411568/Universal_interface_adapter/GPIO.kicad_sch

## KiCad design GPIO.kicad_sch (2026-03-23)

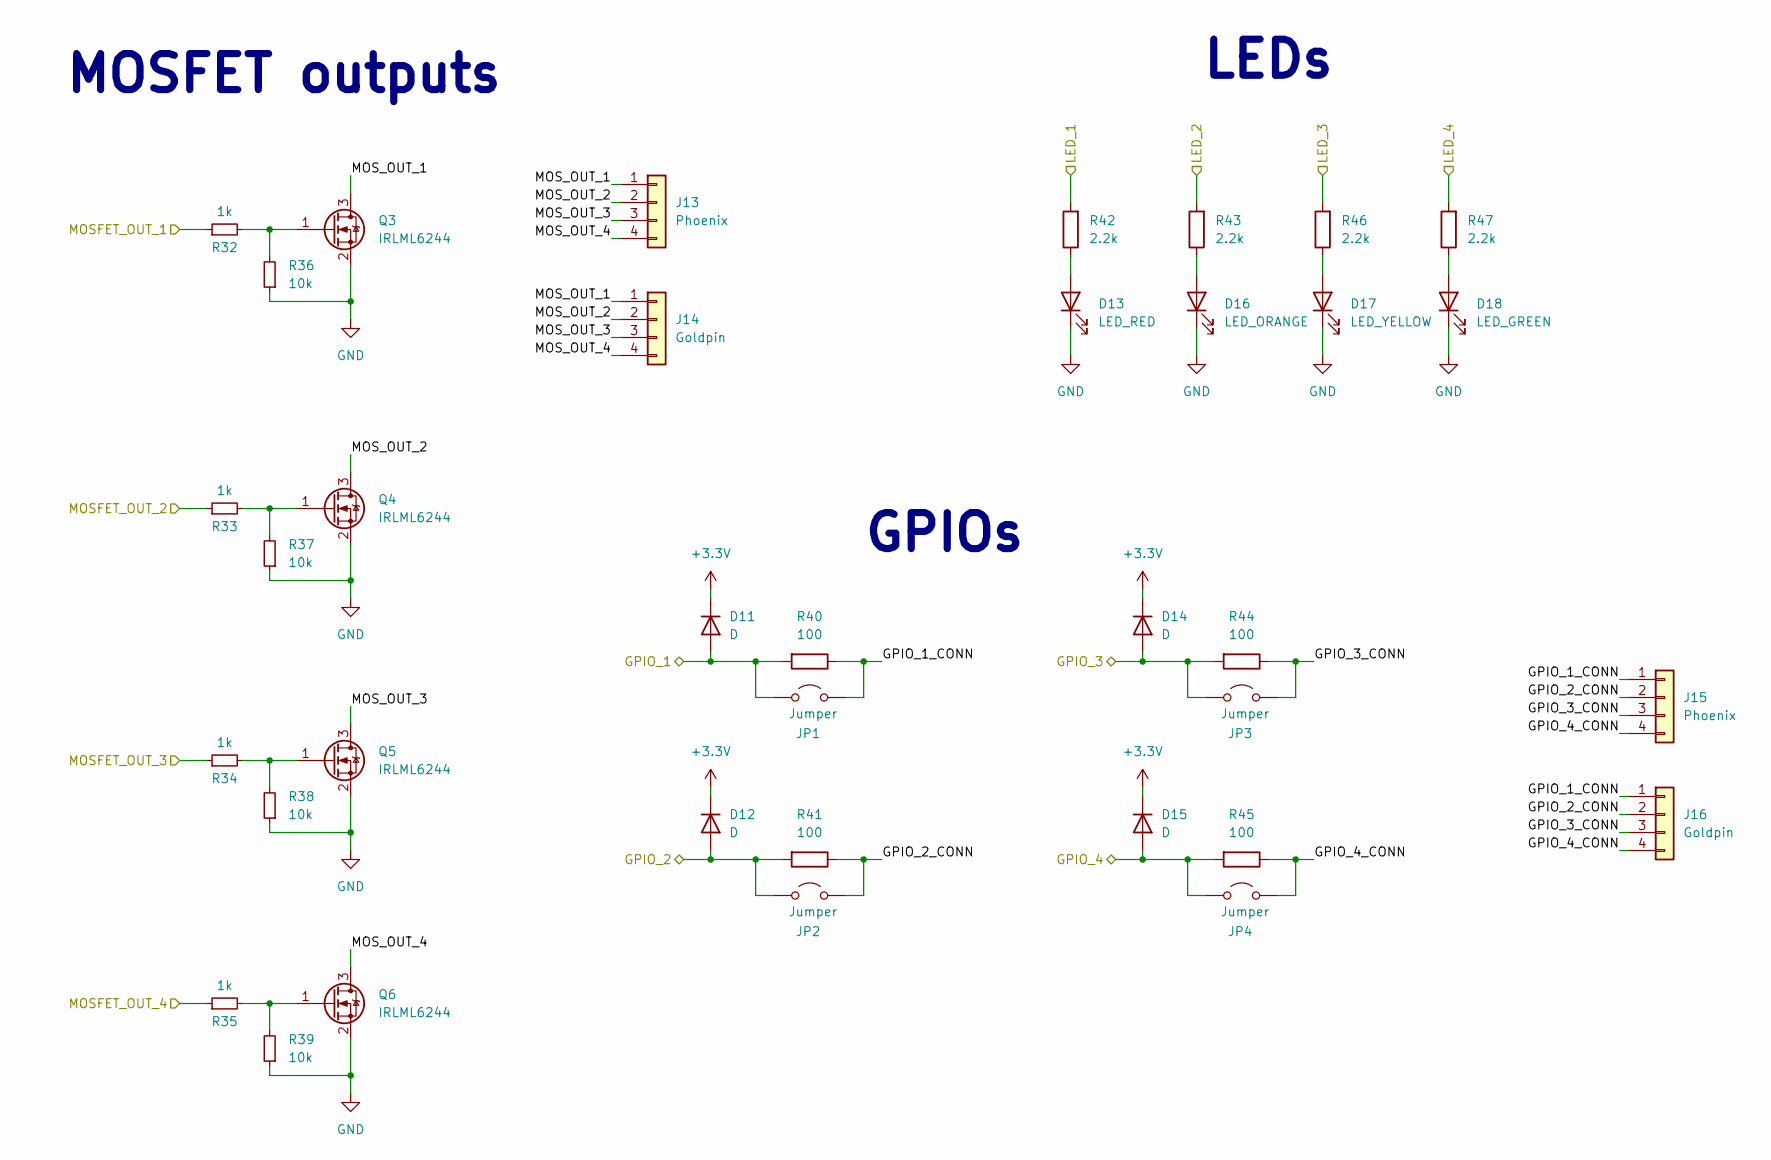
[picture p10: schematic GPIO.kicad_sch]

Parts:
D11, D12, D14, D15: D; D_SMA_Handsoldering
D13: LED_RED; LED_0805_2012Metric_Pad1.15x1.40mm_HandSolder
D16: LED_ORANGE; LED_0805_2012Metric_Pad1.15x1.40mm_HandSolder
D17: LED_YELLOW; LED_0805_2012Metric_Pad1.15x1.40mm_HandSolder
D18: LED_GREEN; LED_0805_2012Metric_Pad1.15x1.40mm_HandSolder
J13, J15: Phoenix; PhoenixContact_MC_1,5_4-G-3.5_1x04_P3.50mm_Horizontal
J14, J16: Goldpin; PinHeader_1x04_P2.54mm_Vertical
JP1, JP2, JP3, JP4: Jumper; PinHeader_1x02_P2.54mm_Vertical
Q3, Q4, Q5, Q6: IRLML6244; SOT-23
R32, R33, R34, R35: 1k; R_0805_2012Metric_Pad1.20x1.40mm_HandSolder
R36, R37, R38, R39: 10k; R_0805_2012Metric_Pad1.20x1.40mm_HandSolder
R40, R41, R44, R45: 100; R_0805_2012Metric_Pad1.20x1.40mm_HandSolder
R42, R43, R46, R47: 2.2k; R_0805_2012Metric_Pad1.20x1.40mm_HandSolder

Connections:
+3.3V: D11.1 (K), D12.1 (K), D14.1 (K), D15.1 (K)
GND: D13.1 (K), D16.1 (K), D17.1 (K), D18.1 (K), Q3.2 (S), Q4.2 (S), Q5.2 (S), Q6.2 (S), R36.1, R37.1, R38.1, R39.1
GPIO_1: D11.2 (A), JP1.1 (A), R40.2
GPIO_1_CONN: J15.1, J16.1, JP1.2 (B), R40.1
GPIO_2: D12.2 (A), JP2.1 (A), R41.2
GPIO_2_CONN: J15.2, J16.2, JP2.2 (B), R41.1
GPIO_3: D14.2 (A), JP3.1 (A), R44.2
GPIO_3_CONN: J15.3, J16.3, JP3.2 (B), R44.1
GPIO_4: D15.2 (A), JP4.1 (A), R45.2
GPIO_4_CONN: J15.4, J16.4, JP4.2 (B), R45.1
LED_1: R42.2
LED_2: R43.2
LED_3: R46.2
LED_4: R47.2
MOSFET_OUT_1: R32.1
MOSFET_OUT_2: R33.1
MOSFET_OUT_3: R34.1
MOSFET_OUT_4: R35.1
MOS_OUT_1: J13.1, J14.1, Q3.3 (D)
MOS_OUT_2: J13.2, J14.2, Q4.3 (D)
MOS_OUT_3: J13.3, J14.3, Q5.3 (D)
MOS_OUT_4: J13.4, J14.4, Q6.3 (D)
unnamed: D13.2 (A), R42.1
unnamed: D16.2 (A), R43.1
unnamed: D17.2 (A), R46.1
unnamed: D18.2 (A), R47.1
unnamed: Q3.1 (G), R32.2, R36.2
unnamed: Q4.1 (G), R33.2, R37.2
unnamed: Q5.1 (G), R34.2, R38.2
unnamed: Q6.1 (G), R35.2, R39.2

Notes on the sheet:
MOSFET outputs
GPIOs
LEDs
