411568/Universal_interface_adapter/analog.kicad_sch

## KiCad design analog.kicad_sch (2026-03-23)

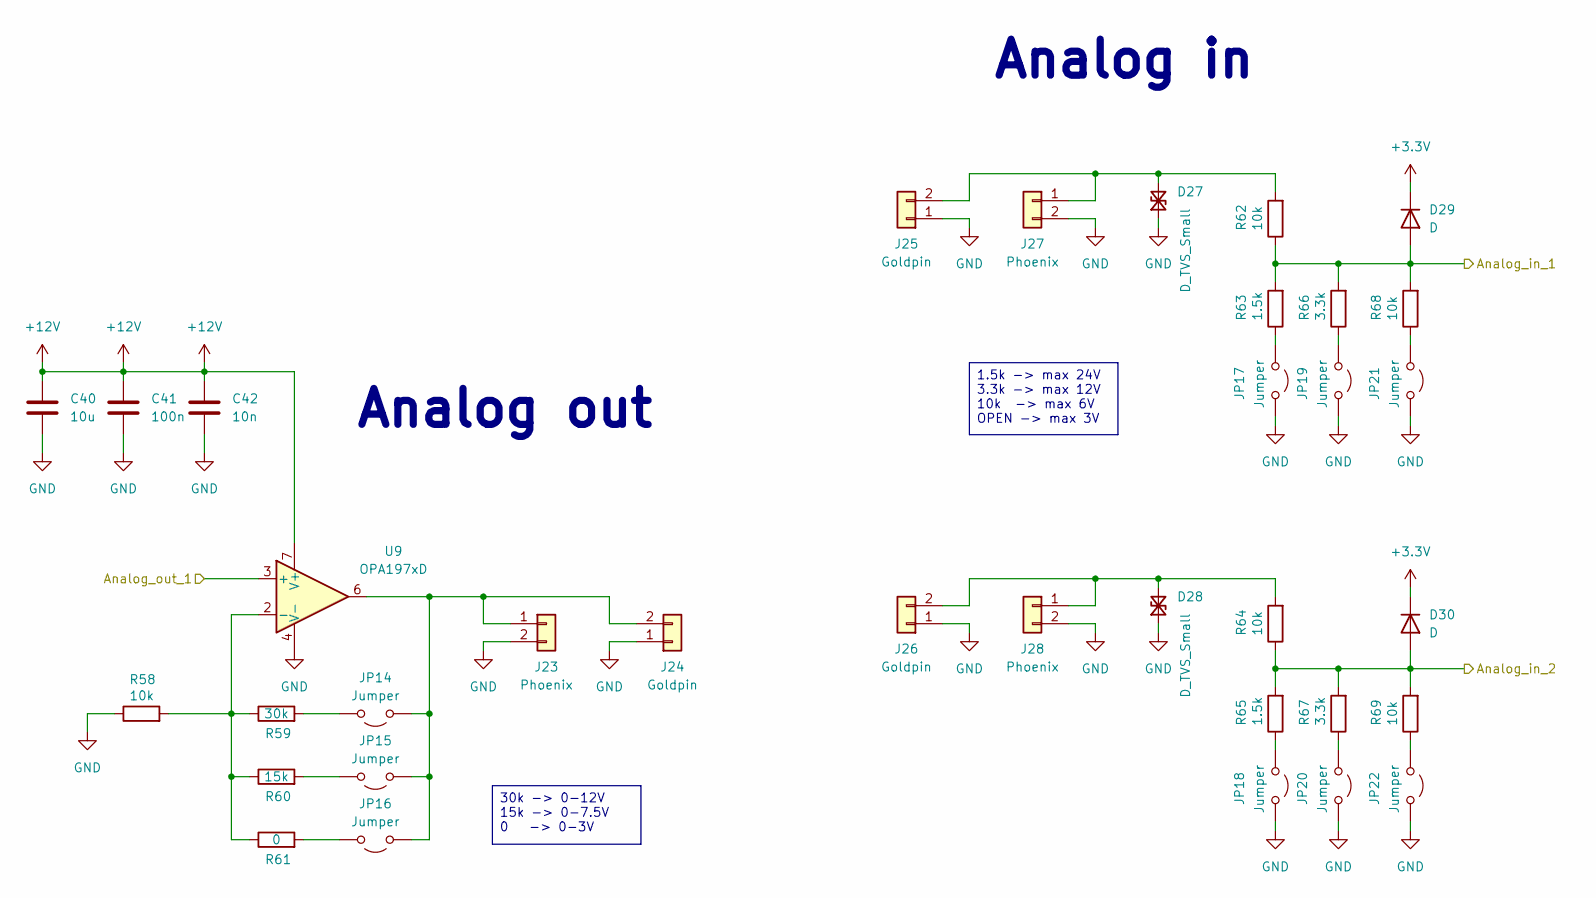
[picture p11: schematic analog.kicad_sch]

Parts:
C40: 10u; C_1206_3216Metric_Pad1.33x1.80mm_HandSolder
C41: 100n; C_1206_3216Metric_Pad1.33x1.80mm_HandSolder
C42: 10n; C_0805_2012Metric_Pad1.18x1.45mm_HandSolder
D27, D28: D_TVS_Small; D_SMA_Handsoldering
D29, D30: D; D_SMA_Handsoldering
J23, J27, J28: Phoenix; PhoenixContact_MC_1,5_2-G-3.5_1x02_P3.50mm_Horizontal
J24, J25, J26: Goldpin; PinHeader_1x02_P2.54mm_Vertical
JP14, JP15, JP16, JP17, JP18, JP19, JP20, JP21, JP22: Jumper; PinHeader_1x02_P2.54mm_Vertical
R58, R62, R64, R68, R69: 10k; R_0805_2012Metric_Pad1.20x1.40mm_HandSolder
R59: 30k; R_0805_2012Metric_Pad1.20x1.40mm_HandSolder
R60: 15k; R_0805_2012Metric_Pad1.20x1.40mm_HandSolder
R61: 0; R_0805_2012Metric_Pad1.20x1.40mm_HandSolder
R63, R65: 1.5k; R_0805_2012Metric_Pad1.20x1.40mm_HandSolder
R66, R67: 3.3k; R_0805_2012Metric_Pad1.20x1.40mm_HandSolder
U9: OPA197xD; SOIC-8_3.9x4.9mm_P1.27mm

Connections:
+3.3V: D29.1 (K), D30.1 (K)
+12V: C40.1, C41.1, C42.1, U9.7 (V+)
Analog_in_1: D29.2 (A), R62.1, R63.2, R66.2, R68.2
Analog_in_2: D30.2 (A), R64.1, R65.2, R67.2, R69.2
Analog_out_1: U9.3 (+)
GND: C40.2, C41.2, C42.2, D27.1 (A1), D28.1 (A1), J23.2, J24.1, J25.1, J26.1, J27.2, J28.2, JP17.2 (B), JP18.2 (B), JP19.2 (B), JP20.2 (B), JP21.2 (B), JP22.2 (B), R58.1, U9.4 (V-)
unnamed: D27.2 (A2), J25.2, J27.1, R62.2
unnamed: D28.2 (A2), J26.2, J28.1, R64.2
unnamed: J23.1, J24.2, JP14.1 (A), JP15.1 (A), JP16.1 (A), U9.6
unnamed: JP14.2 (B), R59.2
unnamed: JP15.2 (B), R60.2
unnamed: JP16.2 (B), R61.2
unnamed: JP17.1 (A), R63.1
unnamed: JP18.1 (A), R65.1
unnamed: JP19.1 (A), R66.1
unnamed: JP20.1 (A), R67.1
unnamed: JP21.1 (A), R68.1
unnamed: JP22.1 (A), R69.1
unnamed: R58.2, R59.1, R60.1, R61.1, U9.2 (-)

Notes on the sheet:
Analog out
Analog in
30k -> 0-12V 15k -> 0-7.5V 0 -> 0-3V
1.5k -> max 24V 3.3k -> max 12V 10k -> max 6V OPEN -> max 3V
