411568/Universal_interface_adapter/can.kicad_sch

## KiCad design can.kicad_sch (2026-03-23)

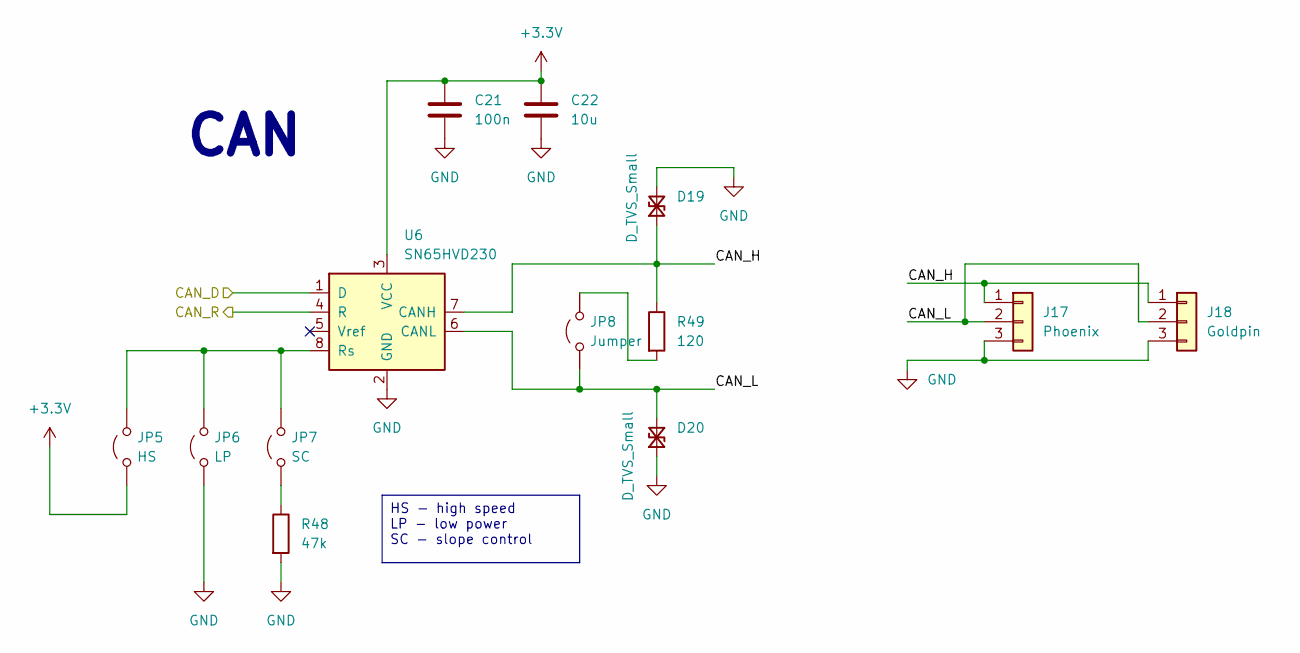
[picture p12: schematic can.kicad_sch]

Parts:
C21: 100n; C_0805_2012Metric_Pad1.18x1.45mm_HandSolder
C22: 10u; C_0805_2012Metric_Pad1.18x1.45mm_HandSolder
D19, D20: D_TVS_Small; D_SMA_Handsoldering
J17: Phoenix; PhoenixContact_MC_1,5_3-G-3.5_1x03_P3.50mm_Horizontal
J18: Goldpin; PinHeader_1x03_P2.54mm_Vertical
JP5: HS; PinHeader_1x02_P2.54mm_Vertical
JP6: LP; PinHeader_1x02_P2.54mm_Vertical
JP7: SC; PinHeader_1x02_P2.54mm_Vertical
JP8: Jumper; PinHeader_1x02_P2.54mm_Vertical
R48: 47k; R_1206_3216Metric_Pad1.30x1.75mm_HandSolder
R49: 120; R_1206_3216Metric_Pad1.30x1.75mm_HandSolder
U6: SN65HVD230; SOIC-8_3.9x4.9mm_P1.27mm

Connections:
+3.3V: C21.1, C22.1, JP5.1 (A), U6.3 (VCC)
CAN_D: U6.1 (D)
CAN_H: D19.1 (A1), J17.1, J18.1, R49.1, U6.7 (CANH)
CAN_L: D20.2 (A2), J17.2, J18.2, JP8.1 (A), U6.6 (CANL)
CAN_R: U6.4 (R)
GND: C21.2, C22.2, D19.2 (A2), D20.1 (A1), J17.3, J18.3, JP6.1 (A), R48.2, U6.2 (GND)
unnamed: JP5.2 (B), JP6.2 (B), JP7.2 (B), U6.8 (Rs)
unnamed: JP7.1 (A), R48.1
unnamed: JP8.2 (B), R49.2

Notes on the sheet:
CAN
HS - high speed LP - low power SC - slope control
