411568/Universal_interface_adapter/isolated_inputs.kicad_sch

## KiCad design isolated_inputs.kicad_sch (2026-03-23)

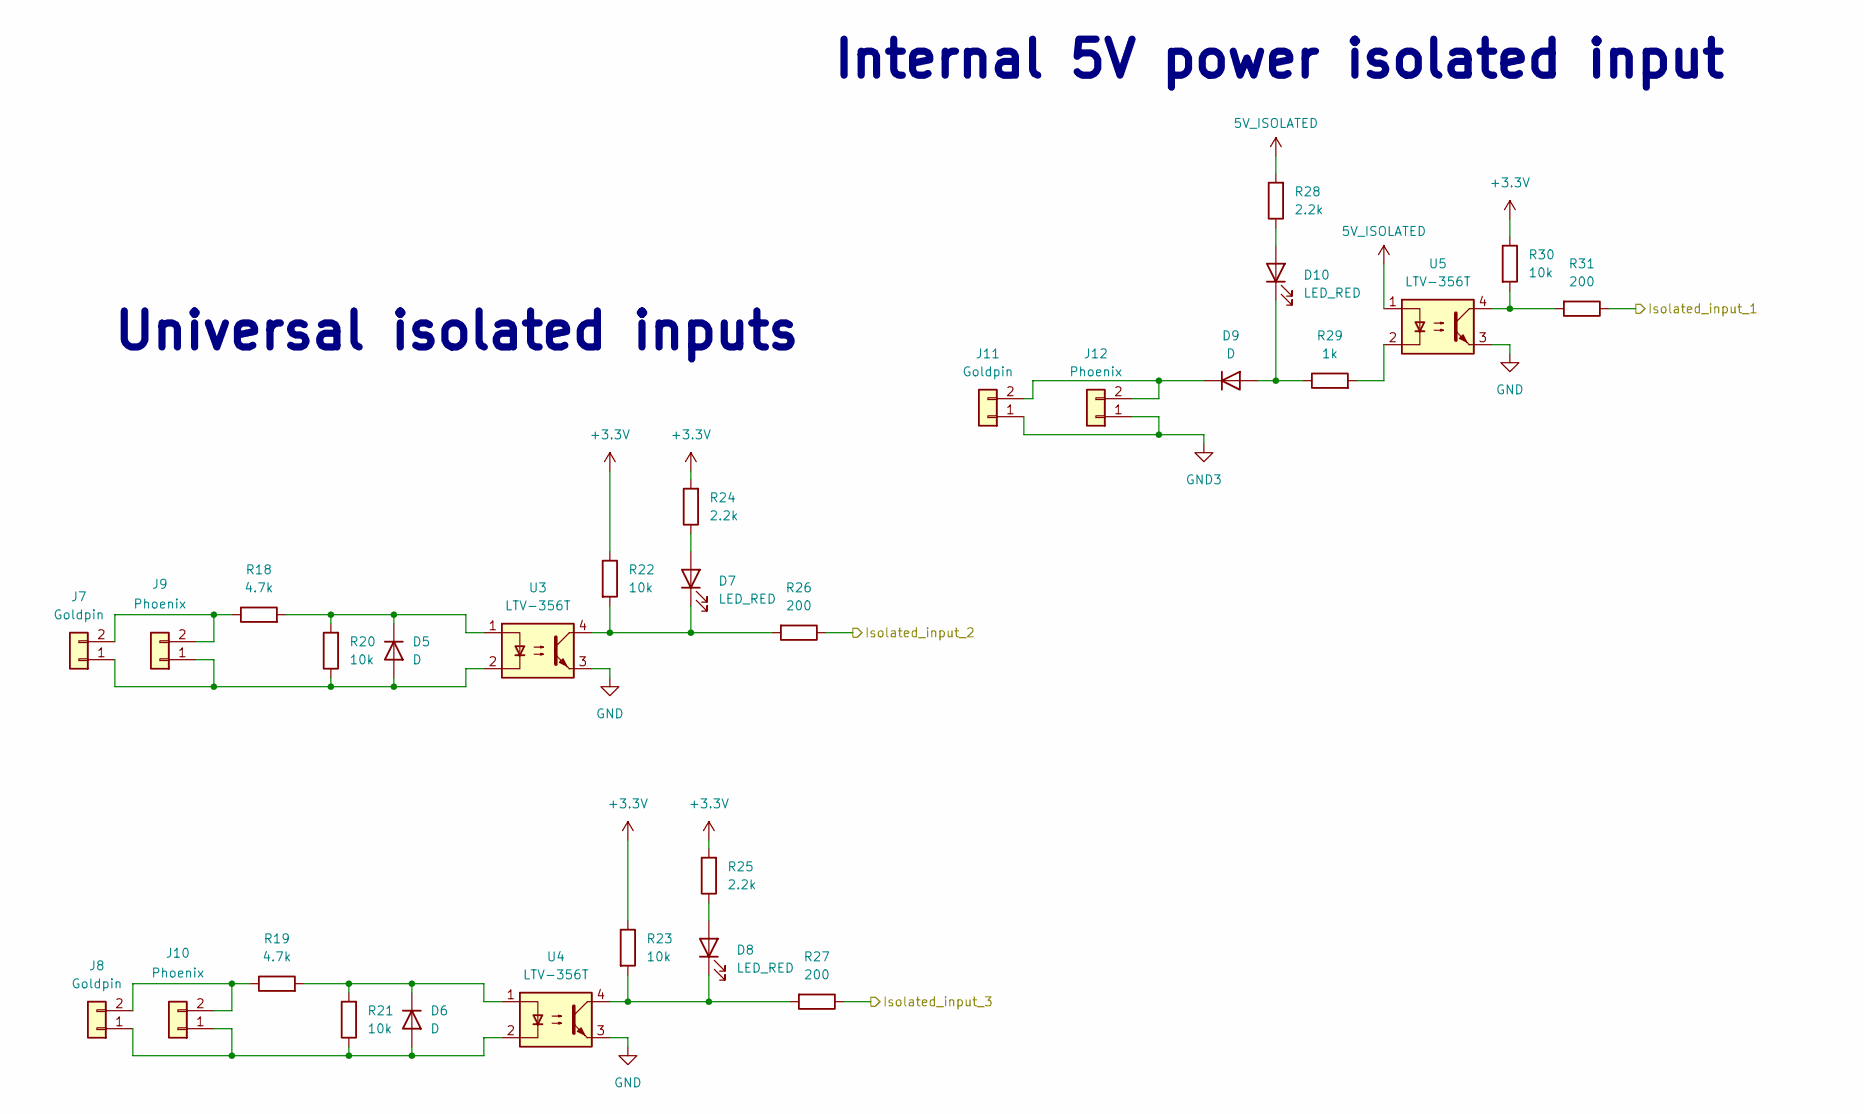
[picture p13: schematic isolated_inputs.kicad_sch]

Parts:
D5, D6, D9: D; D_SMA_Handsoldering
D7, D8, D10: LED_RED; LED_0805_2012Metric_Pad1.15x1.40mm_HandSolder
J7, J8, J11: Goldpin; PinHeader_1x02_P2.54mm_Vertical
J9, J10, J12: Phoenix; PhoenixContact_MC_1,5_2-G-3.5_1x02_P3.50mm_Horizontal
R18, R19: 4.7k; R_0805_2012Metric_Pad1.20x1.40mm_HandSolder
R20, R21, R22, R23, R30: 10k; R_0805_2012Metric_Pad1.20x1.40mm_HandSolder
R24, R25, R28: 2.2k; R_0805_2012Metric_Pad1.20x1.40mm_HandSolder
R26, R27, R31: 200; R_0805_2012Metric_Pad1.20x1.40mm_HandSolder
R29: 1k; R_0805_2012Metric_Pad1.20x1.40mm_HandSolder
U3, U4, U5: LTV-356T; SO-4_4.4x3.6mm_P2.54mm

Connections:
5V_ISOLATED: R28.2, U5.1
+3.3V: R22.1, R23.1, R24.2, R25.2, R30.1
GND: U3.3, U4.3, U5.3
GND3: J11.1, J12.1
Isolated_input_1: R31.1
Isolated_input_2: R26.1
Isolated_input_3: R27.1
unnamed: D5.1 (K), R18.2, R20.2, U3.1
unnamed: D5.2 (A), J7.1, J9.1, R20.1, U3.2
unnamed: D6.1 (K), R19.2, R21.2, U4.1
unnamed: D6.2 (A), J8.1, J10.1, R21.1, U4.2
unnamed: D7.1 (K), R22.2, R26.2, U3.4
unnamed: D7.2 (A), R24.1
unnamed: D8.1 (K), R23.2, R27.2, U4.4
unnamed: D8.2 (A), R25.1
unnamed: D9.1 (K), J11.2, J12.2
unnamed: D9.2 (A), D10.1 (K), R29.1
unnamed: D10.2 (A), R28.1
unnamed: J7.2, J9.2, R18.1
unnamed: J8.2, J10.2, R19.1
unnamed: R29.2, U5.2
unnamed: R30.2, R31.2, U5.4

Notes on the sheet:
Universal isolated inputs
Internal 5V power isolated input
