411568/Universal_interface_adapter/power.kicad_sch

## KiCad design power.kicad_sch (2026-03-23)

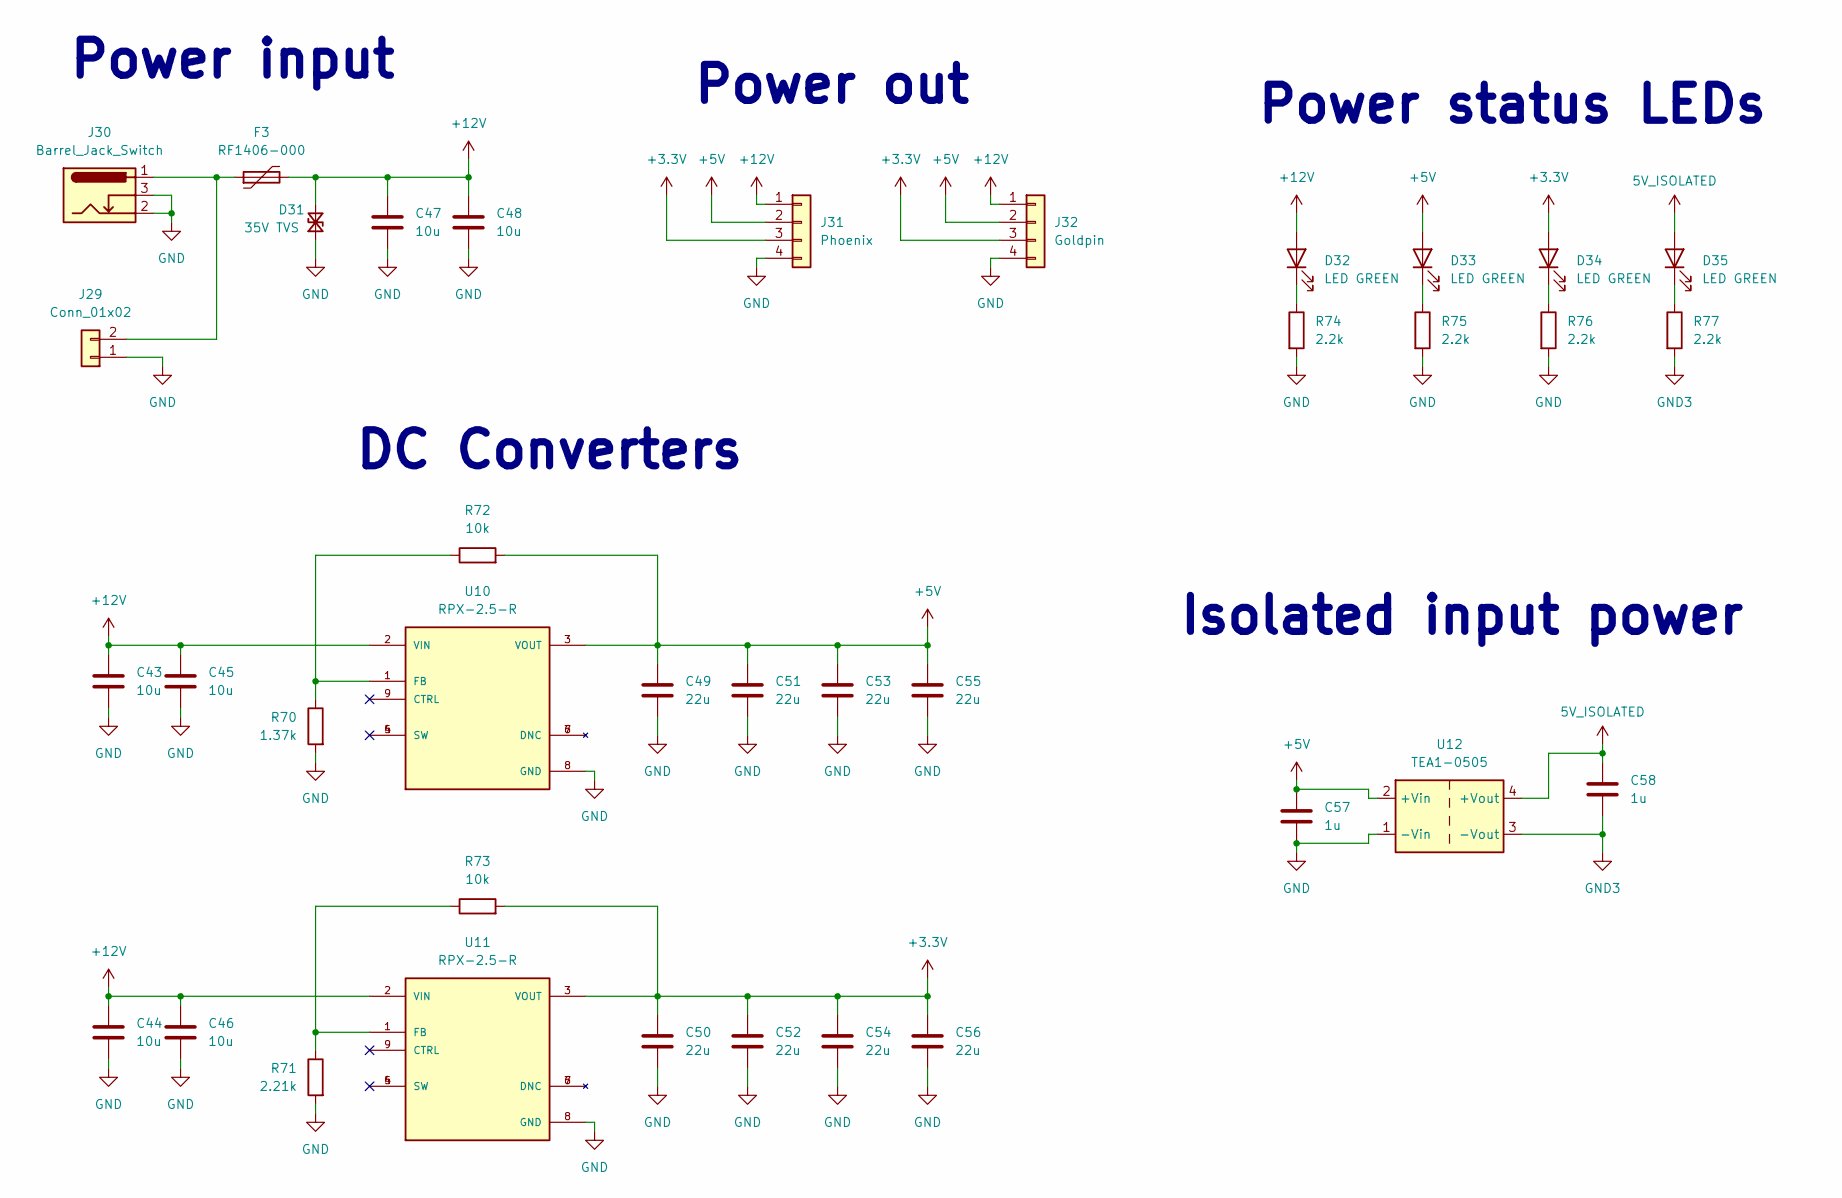
[picture p14: schematic power.kicad_sch]

Parts:
C43, C44, C45, C46, C47, C48: 10u; C_1206_3216Metric_Pad1.33x1.80mm_HandSolder
C49, C50, C51, C52: 22u; C_1206_3216Metric_Pad1.33x1.80mm_HandSolder
C53, C54, C55, C56: 22u; C_0805_2012Metric_Pad1.18x1.45mm_HandSolder
C57, C58: 1u; C_0805_2012Metric_Pad1.18x1.45mm_HandSolder
D31: 35V TVS; D_SMA_Handsoldering
D32, D33, D34, D35: LED GREEN; LED_0805_2012Metric_Pad1.15x1.40mm_HandSolder
F3: RF1406-000; Fuse_1812_4532Metric_Pad1.30x3.40mm_HandSolder
J29: Conn_01x02; PhoenixContact_MC_1,5_2-G-3.5_1x02_P3.50mm_Horizontal
J30: Barrel_Jack_Switch; BarrelJack_GCT_DCJ200-10-A_Horizontal
J31: Phoenix; PhoenixContact_MC_1,5_4-G-3.5_1x04_P3.50mm_Horizontal
J32: Goldpin; PinHeader_1x04_P2.54mm_Vertical
R70: 1.37k; R_0805_2012Metric_Pad1.20x1.40mm_HandSolder
R71: 2.21k; R_0805_2012Metric_Pad1.20x1.40mm_HandSolder
R72, R73: 10k; R_0805_2012Metric_Pad1.20x1.40mm_HandSolder
R74, R75, R76, R77: 2.2k; R_0805_2012Metric_Pad1.20x1.40mm_HandSolder
U10, U11: RPX-2.5-R; CONV_RPX-2.5-R; PARTREV 03/2020
U12: TEA1-0505; Converter_DCDC_TRACO_TEA1-xxxx_THT

Connections:
5V_ISOLATED: C58.1, D35.2 (A), U12.4 (+Vout)
+3.3V: C50.1, C52.1, C54.1, C56.1, D34.2 (A), J31.3, J32.3, R73.2, U11.3 (VOUT)
+5V: C49.1, C51.1, C53.1, C55.1, C57.1, D33.2 (A), J31.2, J32.2, R72.2, U10.3 (VOUT), U12.2 (+Vin)
+12V: C43.1, C44.1, C45.1, C46.1, C47.1, C48.1, D31.2 (A2), D32.2 (A), F3.2, J31.1, J32.1, U10.2 (VIN), U11.2 (VIN)
GND: C43.2, C44.2, C45.2, C46.2, C47.2, C48.2, C49.2, C50.2, C51.2, C52.2, C53.2, C54.2, C55.2, C56.2, C57.2, D31.1 (A1), J29.1, J30.2, J30.3, J31.4, J32.4, R70.2, R71.2, R74.2, R75.2, R76.2, U10.8 (GND), U11.8 (GND), U12.1 (-Vin)
GND3: C58.2, R77.2, U12.3 (-Vout)
unnamed: D32.1 (K), R74.1
unnamed: D33.1 (K), R75.1
unnamed: D34.1 (K), R76.1
unnamed: D35.1 (K), R77.1
unnamed: F3.1, J29.2, J30.1
unnamed: R70.1, R72.1, U10.1 (FB)
unnamed: R71.1, R73.1, U11.1 (FB)
unnamed: U10.4 (SW), U10.5 (SW)
unnamed: U10.6 (DNC), U10.7 (DNC)
unnamed: U11.4 (SW), U11.5 (SW)
unnamed: U11.6 (DNC), U11.7 (DNC)

Notes on the sheet:
Power out
Power input
Power status LEDs
DC Converters
Isolated input power
