411568/Universal_interface_adapter/relay_outputs.kicad_sch

## KiCad design relay_outputs.kicad_sch (2026-03-23)

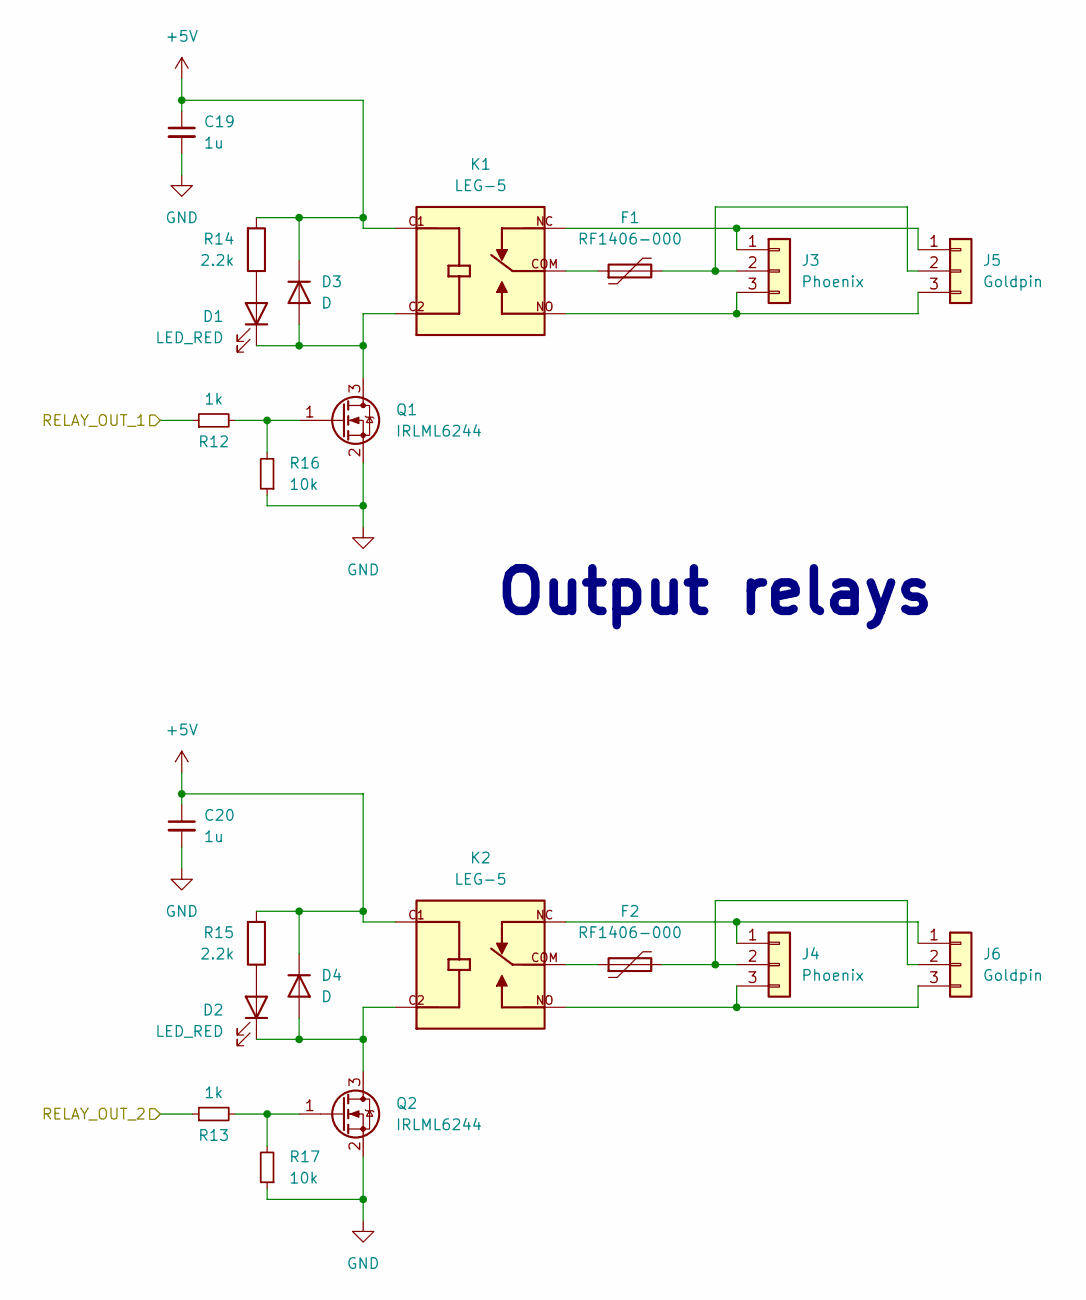
[picture p15: schematic relay_outputs.kicad_sch]

Parts:
C19, C20: 1u; C_0805_2012Metric_Pad1.18x1.45mm_HandSolder
D1, D2: LED_RED; LED_0805_2012Metric_Pad1.15x1.40mm_HandSolder
D3, D4: D; D_SMA_Handsoldering
F1, F2: RF1406-000; Fuse_1812_4532Metric_Pad1.30x3.40mm_HandSolder
J3, J4: Phoenix; PhoenixContact_MC_1,5_3-G-3.5_1x03_P3.50mm_Horizontal
J5, J6: Goldpin; PinHeader_1x03_P2.54mm_Vertical
K1, K2: LEG-5; RELAY_LEG-24; PARTREV N/A
Q1, Q2: IRLML6244; SOT-23
R12, R13: 1k; R_0805_2012Metric_Pad1.20x1.40mm_HandSolder
R14, R15: 2.2k; R_0805_2012Metric_Pad1.20x1.40mm_HandSolder
R16, R17: 10k; R_0805_2012Metric_Pad1.20x1.40mm_HandSolder

Connections:
+5V: C19.1, C20.1, D3.1 (K), D4.1 (K), K1.C1, K2.C1, R14.2, R15.2
GND: C19.2, C20.2, Q1.2 (S), Q2.2 (S), R16.1, R17.1
unnamed: D1.1 (K), D3.2 (A), K1.C2, Q1.3 (D)
unnamed: D1.2 (A), R14.1
unnamed: D2.1 (K), D4.2 (A), K2.C2, Q2.3 (D)
unnamed: D2.2 (A), R15.1
unnamed: F1.1, K1.COM
unnamed: F1.2, J3.2, J5.2
unnamed: F2.1, K2.COM
unnamed: F2.2, J4.2, J6.2
unnamed: J3.1, J5.1, K1.NC
unnamed: J3.3, J5.3, K1.NO
unnamed: J4.1, J6.1, K2.NC
unnamed: J4.3, J6.3, K2.NO
unnamed: Q1.1 (G), R12.2, R16.2
unnamed: Q2.1 (G), R13.2, R17.2
RELAY_OUT_1: R12.1
RELAY_OUT_2: R13.1

Notes on the sheet:
Output relays
