411568/Universal_interface_adapter/rs422_485_232.kicad_sch

## KiCad design rs422_485_232.kicad_sch (2026-03-23)

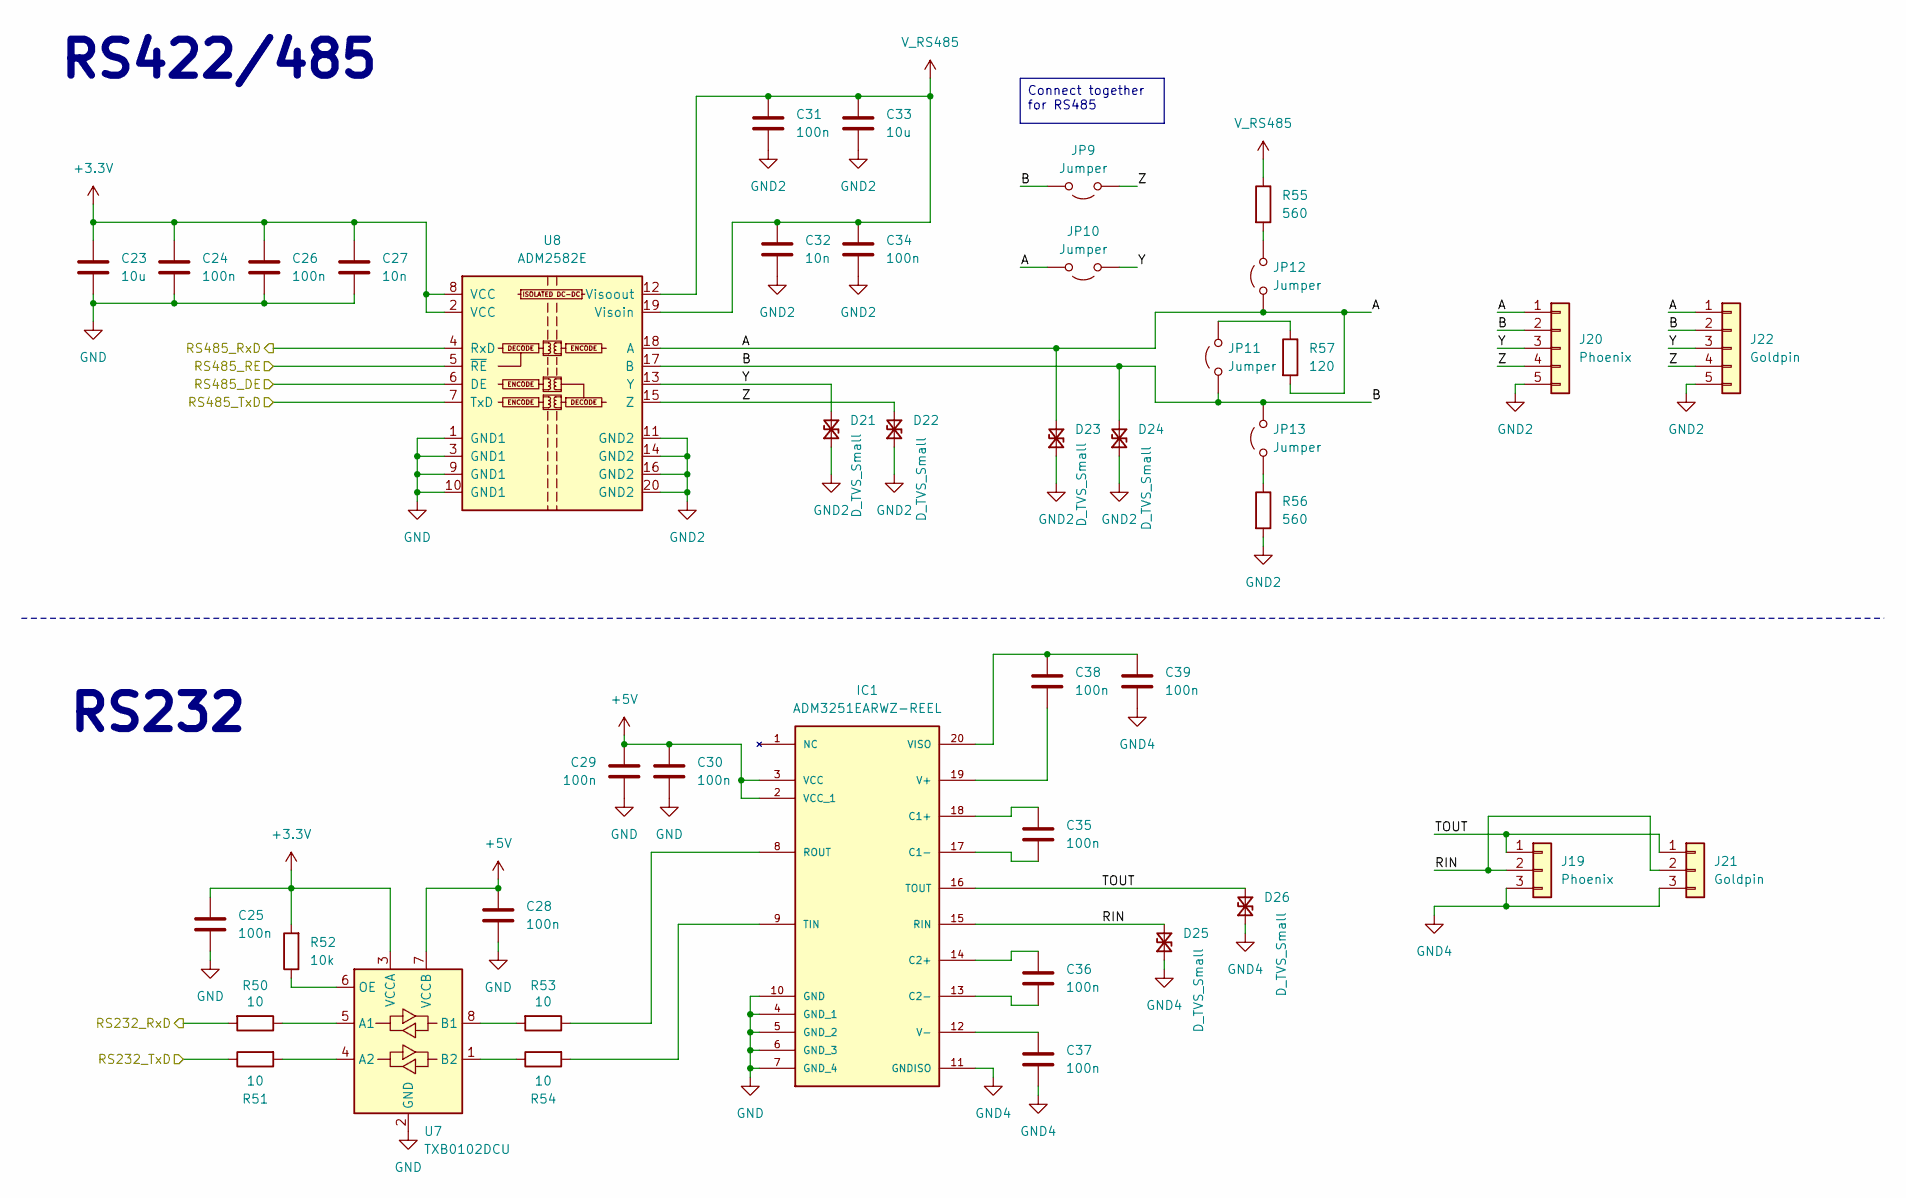
[picture p16: schematic rs422_485_232.kicad_sch]

Parts:
C23, C33: 10u; C_0805_2012Metric_Pad1.18x1.45mm_HandSolder
C24, C25, C26, C28, C29, C30, C31, C34, C35, C36, C37, C38, C39: 100n; C_0805_2012Metric_Pad1.18x1.45mm_HandSolder
C27, C32: 10n; C_0805_2012Metric_Pad1.18x1.45mm_HandSolder
D21, D22, D23, D24, D25, D26: D_TVS_Small; D_SMA_Handsoldering
IC1: ADM3251EARWZ-REEL; SOIC127P1032X265-20N; MOUSER_PART_NUMBER 584-ADM3251EARWZ-R
J19: Phoenix; PhoenixContact_MC_1,5_3-G-3.5_1x03_P3.50mm_Horizontal
J20: Phoenix; PhoenixContact_MC_1,5_5-G-3.5_1x05_P3.50mm_Horizontal
J21: Goldpin; PinHeader_1x03_P2.54mm_Vertical
J22: Goldpin; PinHeader_1x05_P2.54mm_Vertical
JP9, JP10, JP11, JP12, JP13: Jumper; PinHeader_1x02_P2.54mm_Vertical
R50, R51, R53, R54: 10; R_0805_2012Metric_Pad1.20x1.40mm_HandSolder
R52: 10k; R_0805_2012Metric_Pad1.20x1.40mm_HandSolder
R55, R56: 560; R_1206_3216Metric_Pad1.30x1.75mm_HandSolder
R57: 120; R_1206_3216Metric_Pad1.30x1.75mm_HandSolder
U7: TXB0102DCU; VSSOP-8_2.3x2mm_P0.5mm
U8: ADM2582E; SOIC-20W_7.5x12.8mm_P1.27mm

Connections:
+3.3V: C23.1, C24.1, C25.1, C26.1, C27.1, R52.2, U7.3 (VCCA), U8.2 (VCC), U8.8 (VCC)
+5V: C28.1, C29.1, C30.1, IC1.2 (VCC_1), IC1.3 (VCC), U7.7 (VCCB)
A: D23.2 (A2), J20.1, J22.1, JP10.2 (B), JP12.1 (A), R57.2, U8.18 (A)
B: D24.2 (A2), J20.2, J22.2, JP9.2 (B), JP11.1 (A), JP13.2 (B), U8.17 (B)
GND: C23.2, C24.2, C25.2, C26.2, C27.2, C28.2, C29.2, C30.2, IC1.4 (GND_1), IC1.5 (GND_2), IC1.6 (GND_3), IC1.7 (GND_4), IC1.10 (GND), U7.2 (GND), U8.1 (GND1), U8.3 (GND1), U8.9 (GND1), U8.10 (GND1)
GND2: C31.2, C32.2, C33.2, C34.2, D21.1 (A1), D22.1 (A1), D23.1 (A1), D24.1 (A1), J20.5, J22.5, R56.2, U8.11 (GND2), U8.14 (GND2), U8.16 (GND2), U8.20 (GND2)
GND4: C37.2, C39.2, D25.1 (A1), D26.1 (A1), IC1.11 (GNDISO), J19.3, J21.3
unnamed: C35.1, IC1.18 (C1+)
unnamed: C35.2, IC1.17 (C1-)
unnamed: C36.1, IC1.14 (C2+)
unnamed: C36.2, IC1.13 (C2-)
unnamed: C37.1, IC1.12 (V-)
unnamed: C38.1, C39.1, IC1.20 (VISO)
unnamed: C38.2, IC1.19 (V+)
unnamed: IC1.8 (ROUT), R53.1
unnamed: IC1.9 (TIN), R54.2
unnamed: JP11.2 (B), R57.1
unnamed: JP12.2 (B), R55.2
unnamed: JP13.1 (A), R56.1
unnamed: R50.1, U7.5 (A1)
unnamed: R51.2, U7.4 (A2)
unnamed: R52.1, U7.6 (OE)
unnamed: R53.2, U7.8 (B1)
unnamed: R54.1, U7.1 (B2)
RIN: D25.2 (A2), IC1.15 (RIN), J19.2, J21.2
RS232_RxD: R50.2
RS232_TxD: R51.1
RS485_DE: U8.6 (DE)
RS485_RE: U8.5 (~RE)
RS485_RxD: U8.4 (RxD)
RS485_TxD: U8.7 (TxD)
TOUT: D26.2 (A2), IC1.16 (TOUT), J19.1, J21.1
V_RS485: C31.1, C32.1, C33.1, C34.1, R55.1, U8.12 (Visoout), U8.19 (Visoin)
Y: D21.2 (A2), J20.3, J22.3, JP10.1 (A), U8.13 (Y)
Z: D22.2 (A2), J20.4, J22.4, JP9.1 (A), U8.15 (Z)

Notes on the sheet:
RS422/485
RS232
Connect together for RS485
