411568/Universal_interface_adapter/uart_i2c_spi.kicad_sch

## KiCad design uart_i2c_spi.kicad_sch (2026-03-23)

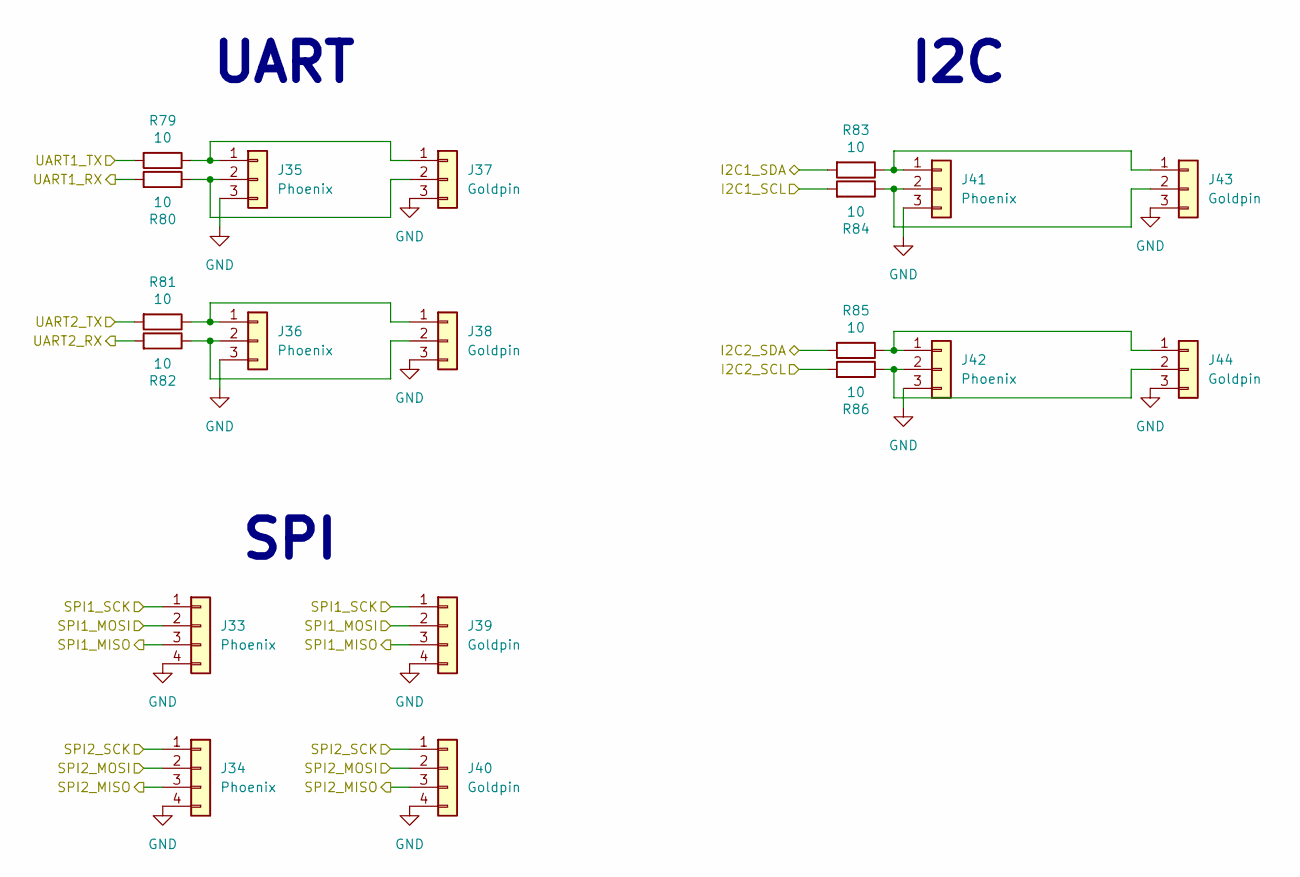
[picture p17: schematic uart_i2c_spi.kicad_sch]

Parts:
J33, J34: Phoenix; PhoenixContact_MC_1,5_4-G-3.5_1x04_P3.50mm_Horizontal
J35, J36, J41, J42: Phoenix; PhoenixContact_MC_1,5_3-G-3.5_1x03_P3.50mm_Horizontal
J37, J38, J43, J44: Goldpin; PinHeader_1x03_P2.54mm_Vertical
J39, J40: Goldpin; PinHeader_1x04_P2.54mm_Vertical
R79, R80, R81, R82, R83, R84, R85, R86: 10; R_0805_2012Metric_Pad1.20x1.40mm_HandSolder

Connections:
GND: J33.4, J34.4, J35.3, J36.3, J37.3, J38.3, J39.4, J40.4, J41.3, J42.3, J43.3, J44.3
I2C1_SCL: R84.2
I2C1_SDA: R83.2
I2C2_SCL: R86.2
I2C2_SDA: R85.2
unnamed: J35.1, J37.1, R79.1
unnamed: J35.2, J37.2, R80.1
unnamed: J36.1, J38.1, R81.1
unnamed: J36.2, J38.2, R82.1
unnamed: J41.1, J43.1, R83.1
unnamed: J41.2, J43.2, R84.1
unnamed: J42.1, J44.1, R85.1
unnamed: J42.2, J44.2, R86.1
SPI1_MISO: J33.3, J39.3
SPI1_MOSI: J33.2, J39.2
SPI1_SCK: J33.1, J39.1
SPI2_MISO: J34.3, J40.3
SPI2_MOSI: J34.2, J40.2
SPI2_SCK: J34.1, J40.1
UART1_RX: R80.2
UART1_TX: R79.2
UART2_RX: R82.2
UART2_TX: R81.2

Notes on the sheet:
I2C
SPI
UART
