411568/Universal_interface_adapter/universal_interface_adapter.kicad_sch

## KiCad design universal_interface_adapter.kicad_sch (2026-03-23)

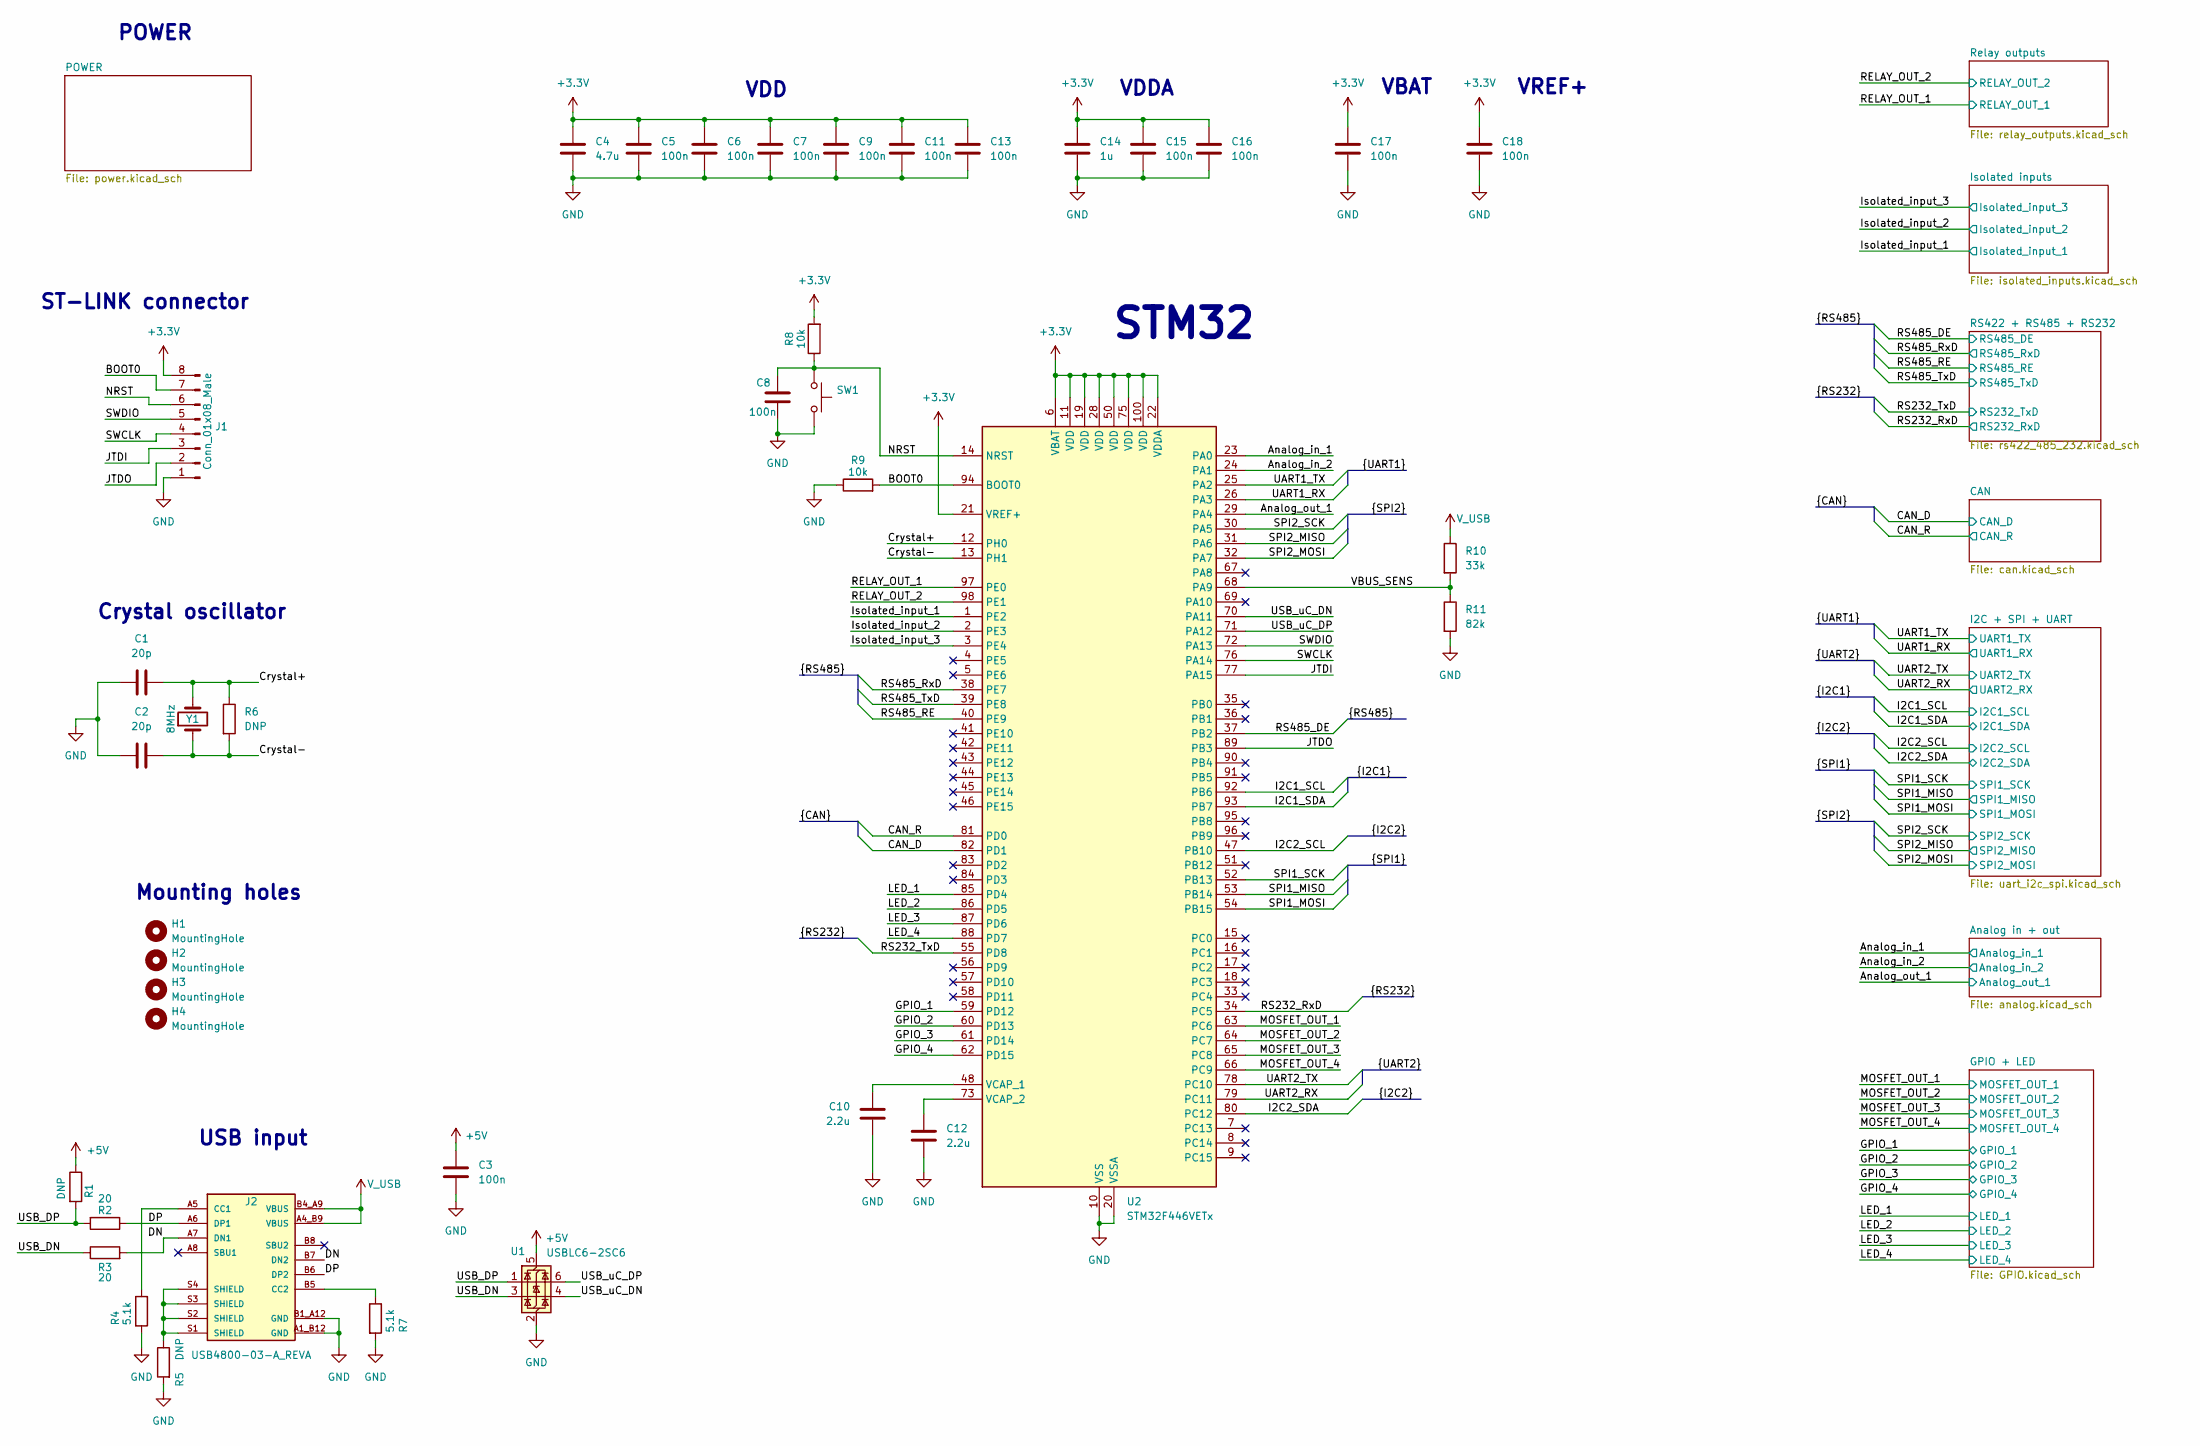
[picture p18: schematic universal_interface_adapter.kicad_sch]

Parts:
C1, C2: 20p; C_0603_1608Metric_Pad1.08x0.95mm_HandSolder
C3, C5, C6, C7, C9, C11, C13, C15, C16, C17, C18: 100n; C_1206_3216Metric_Pad1.33x1.80mm_HandSolder
C4: 4.7u; C_1206_3216Metric_Pad1.33x1.80mm_HandSolder
C8: 100n; C_0805_2012Metric_Pad1.18x1.45mm_HandSolder
C10, C12: 2.2u; C_1206_3216Metric_Pad1.33x1.80mm_HandSolder
C14: 1u; C_1206_3216Metric_Pad1.33x1.80mm_HandSolder
H1, H2, H3, H4: MountingHole; MountingHole_3mm
J1: Conn_01x08_Male; PinHeader_1x08_P2.54mm_Horizontal
J2: USB4800-03-A_REVA; GCT_USB4800-03-A_REVA; PARTREV A
R1, R5, R6: DNP; R_1206_3216Metric_Pad1.30x1.75mm_HandSolder
R2, R3: 20; R_1206_3216Metric_Pad1.30x1.75mm_HandSolder
R4, R7: 5.1k; R_1206_3216Metric_Pad1.30x1.75mm_HandSolder
R8, R9: 10k; R_1206_3216Metric_Pad1.30x1.75mm_HandSolder
R10: 33k; R_1206_3216Metric_Pad1.30x1.75mm_HandSolder
R11: 82k; R_1206_3216Metric_Pad1.30x1.75mm_HandSolder
SW1: SW_Push; SW_SPST_TL3342
U1: USBLC6-2SC6; SOT-23-6
U2: STM32F446VETx; LQFP-100_14x14mm_P0.5mm
Y1: 8MHz; Crystal_SMD_HC49-SD

Connections:
+3.3V: C4.1, C5.1, C6.1, C7.1, C9.1, C11.1, C13.1, C14.1, C15.1, C16.1, C17.1, C18.1, J1.8, R8.2, U2.6 (VBAT), U2.11 (VDD), U2.19 (VDD), U2.21 (VREF+), U2.22 (VDDA), U2.28 (VDD), U2.50 (VDD), U2.75 (VDD), U2.100 (VDD)
+5V: C3.1, R1.1, U1.5 (VBUS)
Analog_in_1: U2.23 (PA0)
Analog_in_2: U2.24 (PA1)
Analog_out_1: U2.29 (PA4)
BOOT0: J1.7, R9.2, U2.94 (BOOT0)
CAN_D: U2.82 (PD1)
CAN_R: U2.81 (PD0)
Crystal+: C1.2, R6.1, U2.12 (PH0), Y1.2
Crystal-: C2.2, R6.2, U2.13 (PH1), Y1.1
DN: J2.A7 (DN1), J2.B7 (DN2), R3.2
DP: J2.A6 (DP1), J2.B6 (DP2), R2.1
GND: C1.1, C2.1, C3.2, C4.2, C5.2, C6.2, C7.2, C8.1, C9.2, C10.2, C11.2, C12.2, C13.2, C14.2, C15.2, C16.2, C17.2, C18.2, J1.1, J2.A1_B12 (GND), J2.B1_A12 (GND), R4.2, R5.2, R7.2, R9.1, R11.2, SW1.2, U1.2 (GND), U2.10 (VSS), U2.20 (VSSA), U2.27 (VSS), U2.49 (VSS), U2.74 (VSS), U2.99 (VSS)
GPIO_1: U2.59 (PD12)
GPIO_2: U2.60 (PD13)
GPIO_3: U2.61 (PD14)
GPIO_4: U2.62 (PD15)
I2C1_SCL: U2.92 (PB6)
I2C1_SDA: U2.93 (PB7)
I2C2_SCL: U2.47 (PB10)
I2C2_SDA: U2.80 (PC12)
Isolated_input_1: U2.1 (PE2)
Isolated_input_2: U2.2 (PE3)
Isolated_input_3: U2.3 (PE4)
JTDI: J1.3, U2.77 (PA15)
JTDO: J1.2, U2.89 (PB3)
LED_1: U2.85 (PD4)
LED_2: U2.86 (PD5)
LED_3: U2.87 (PD6)
LED_4: U2.88 (PD7)
MOSFET_OUT_1: U2.63 (PC6)
MOSFET_OUT_2: U2.64 (PC7)
MOSFET_OUT_3: U2.65 (PC8)
MOSFET_OUT_4: U2.66 (PC9)
NRST: C8.2, J1.6, R8.1, SW1.1, U2.14 (NRST)
unnamed: C10.1, U2.48 (VCAP_1)
unnamed: C12.1, U2.73 (VCAP_2)
unnamed: J2.A5 (CC1), R4.1
unnamed: J2.B5 (CC2), R7.1
unnamed: J2.S1 (SHIELD), J2.S2 (SHIELD), J2.S3 (SHIELD), J2.S4 (SHIELD), R5.1
RELAY_OUT_1: U2.97 (PE0)
RELAY_OUT_2: U2.98 (PE1)
RS232_RxD: U2.34 (PC5)
RS232_TxD: U2.55 (PD8)
RS485_DE: U2.37 (PB2)
RS485_RE: U2.40 (PE9)
RS485_RxD: U2.38 (PE7)
RS485_TxD: U2.39 (PE8)
SPI1_MISO: U2.53 (PB14)
SPI1_MOSI: U2.54 (PB15)
SPI1_SCK: U2.52 (PB13)
SPI2_MISO: U2.31 (PA6)
SPI2_MOSI: U2.32 (PA7)
SPI2_SCK: U2.30 (PA5)
SWCLK: J1.4, U2.76 (PA14)
SWDIO: J1.5, U2.72 (PA13)
UART1_RX: U2.26 (PA3)
UART1_TX: U2.25 (PA2)
UART2_RX: U2.79 (PC11)
UART2_TX: U2.78 (PC10)
USB_DN: R3.1, U1.3 (I/O2)
USB_DP: R1.2, R2.2, U1.1 (I/O1)
USB_uC_DN: U1.4 (I/O2), U2.70 (PA11)
USB_uC_DP: U1.6 (I/O1), U2.71 (PA12)
VBUS_SENS: R10.2, R11.1, U2.68 (PA9)
V_USB: J2.A4_B9 (VBUS), J2.B4_A9 (VBUS), R10.1

Notes on the sheet:
POWER
VDD
STM32
VBAT
Crystal oscillator
Mounting holes
VDDA
ST-LINK connector
VREF+
USB input
